ArnaanShah/VantaPad/ImagesVideos/IMG_0884.webp

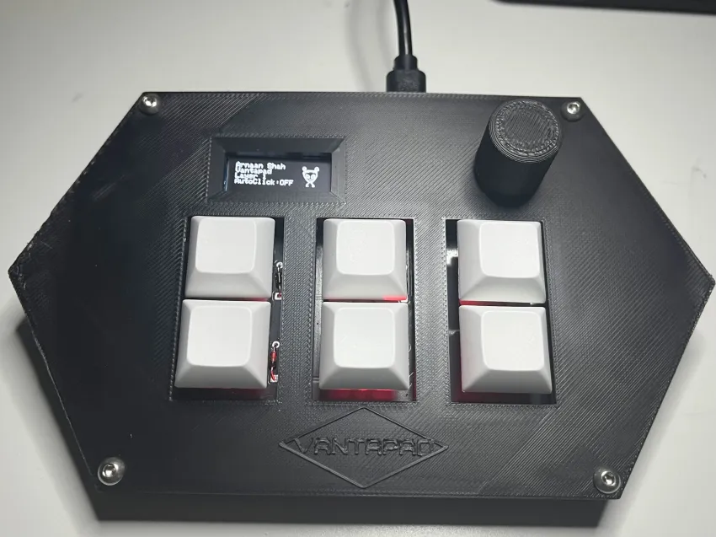
ImagesVideos/IMG_0884.webp
