ArnaanShah/VantaPad/ImagesVideos/IMG_0885.webp

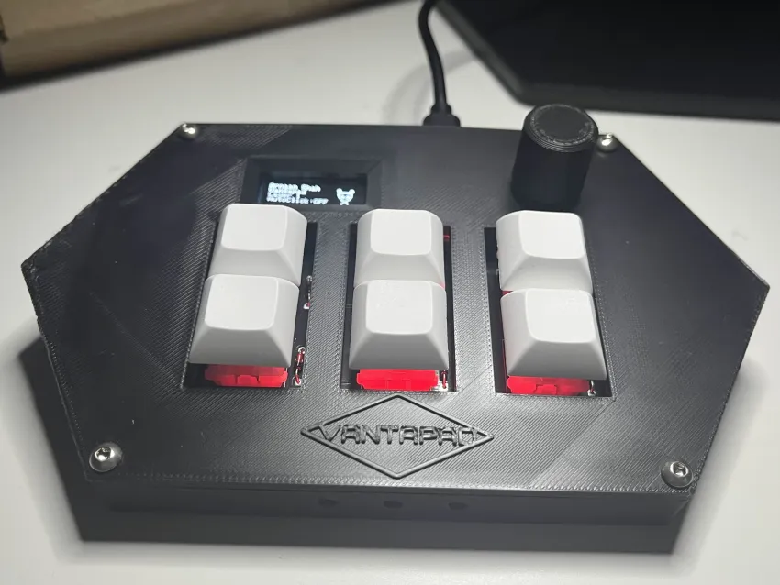
ImagesVideos/IMG_0885.webp
