ArnaanShah/VantaPad/ImagesVideos/IMG_0886.webp

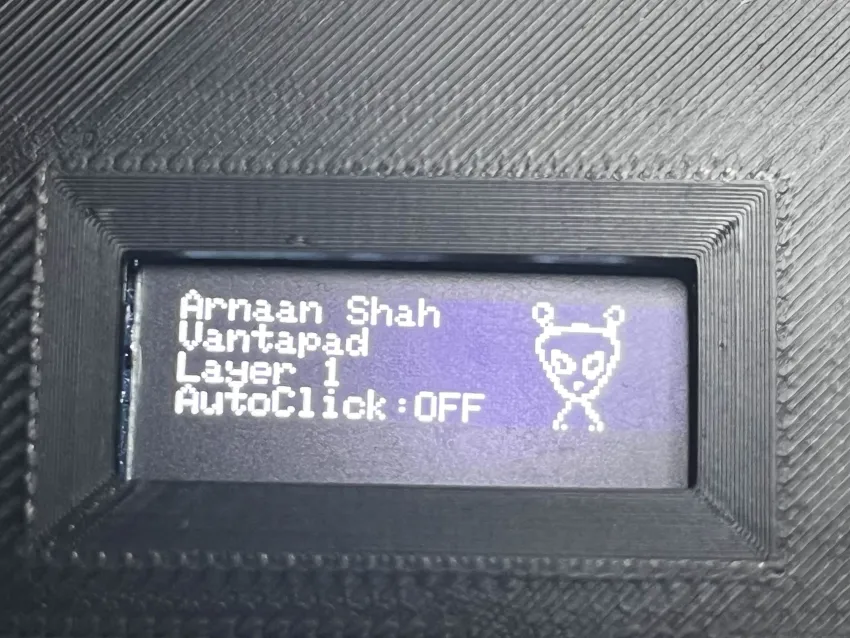
ImagesVideos/IMG_0886.webp
